barkolorious/opaque/report/ekler/PrMd_sch.pdf

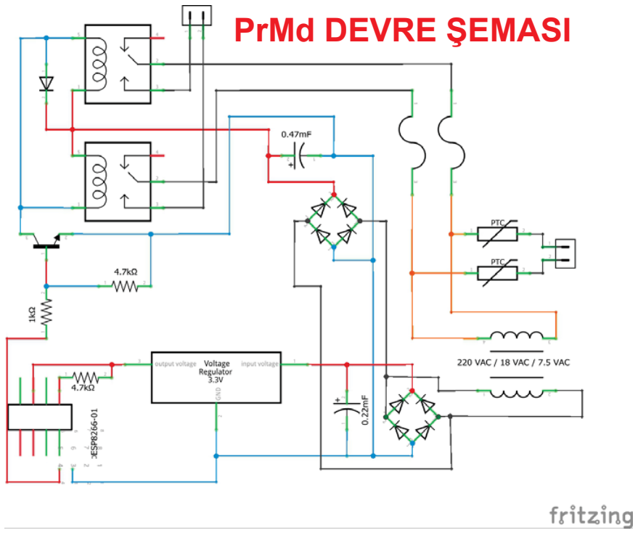
[picture p46: figure]
PrMd DEVRE ùEMASI
