barkolorious/opaque/Resimler/PCB_R4 V2.pdf

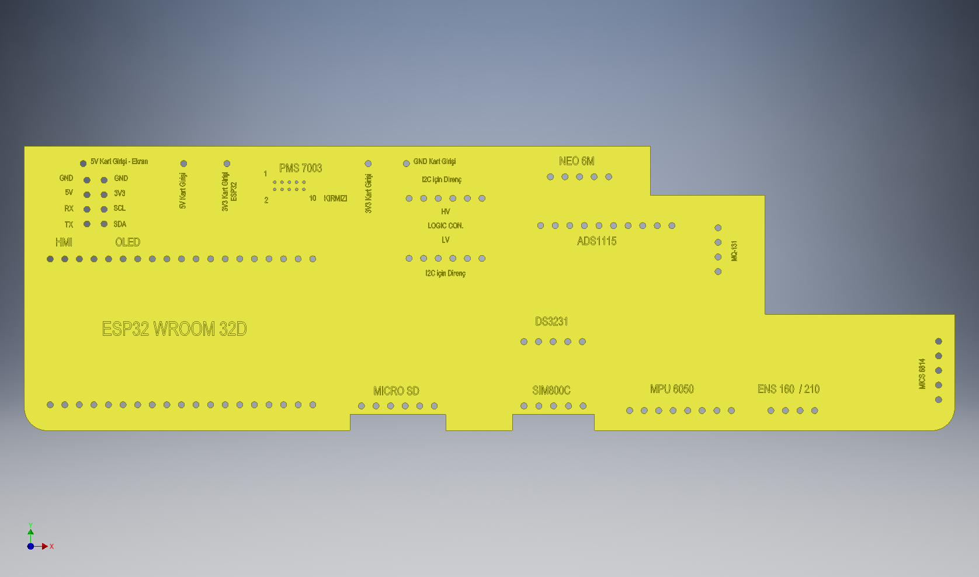
[picture p61: page 1]
