barkolorious/opaque/Notes/assets/20241108_101346.jpg

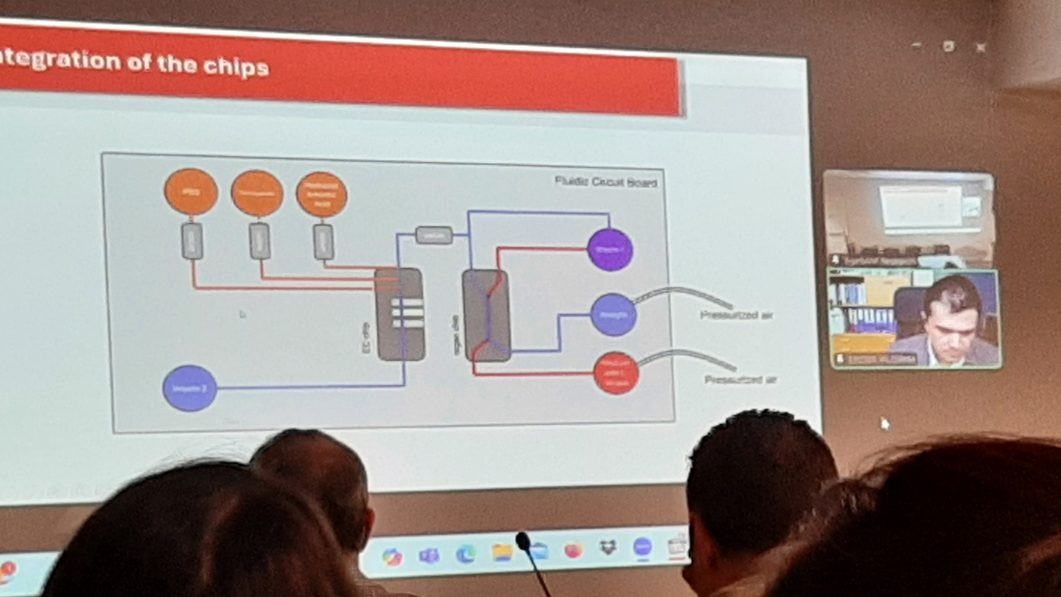
Notes/assets/20241108_101346.jpg
