barkolorious/opaque/Notes/assets/20241108_101506.jpg

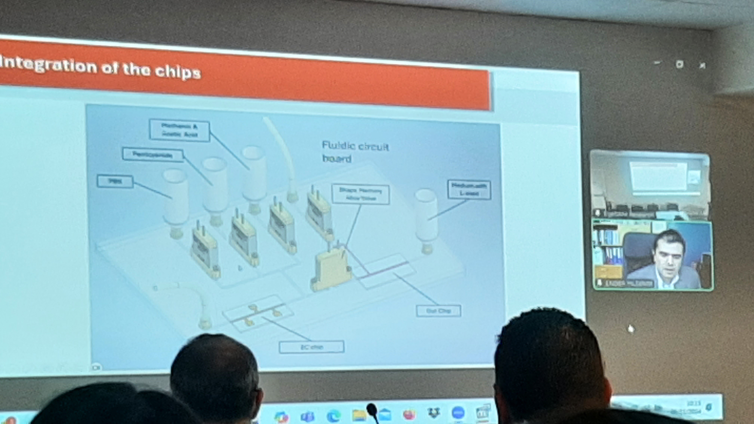
Notes/assets/20241108_101506.jpg
