barkolorious/opaque/Notes/assets/20241108_112509.jpg

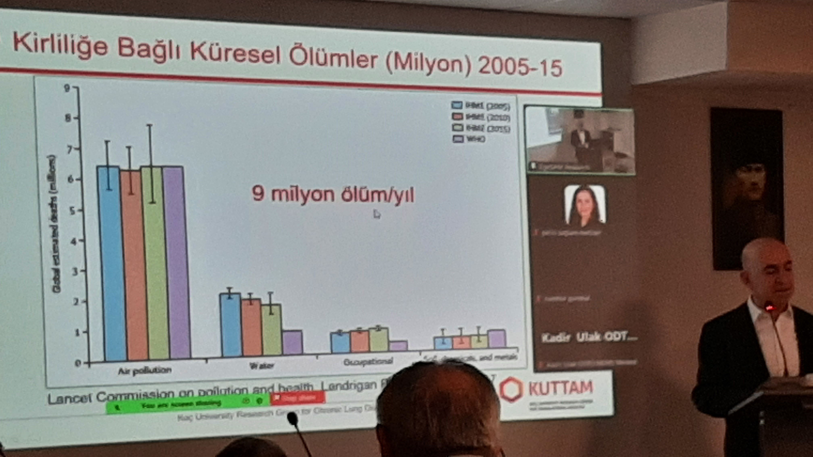
Notes/assets/20241108_112509.jpg
