barkolorious/opaque/Notes/assets/20241108_112550.jpg

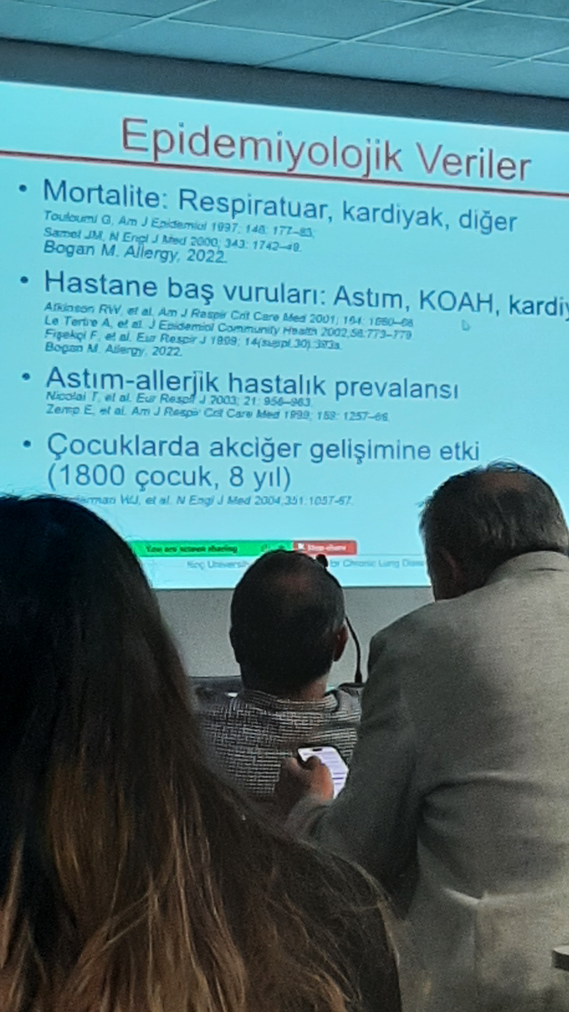
Notes/assets/20241108_112550.jpg
