barkolorious/opaque/Notes/assets/20241108_112724.jpg

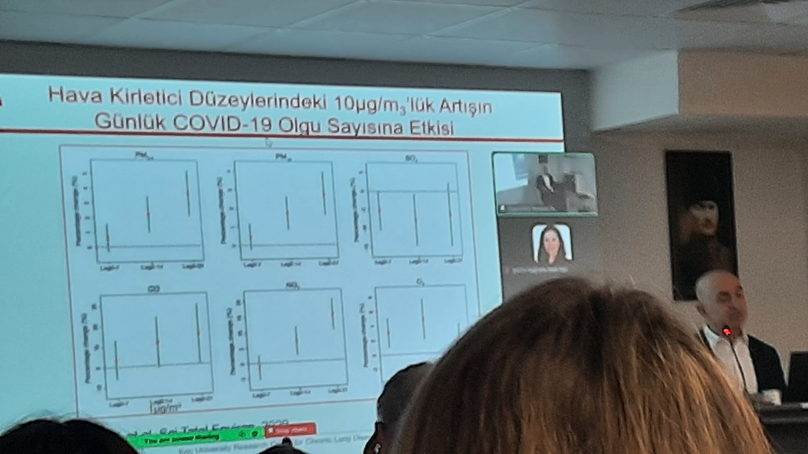
Notes/assets/20241108_112724.jpg
