barkolorious/opaque/Notes/assets/20241108_112844.jpg

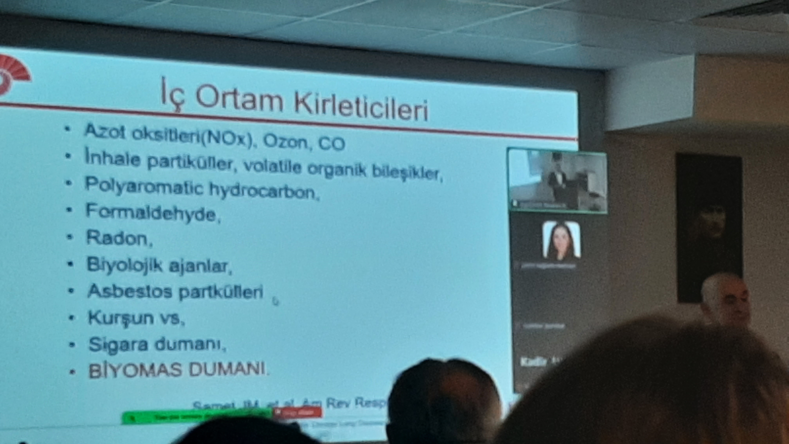
Notes/assets/20241108_112844.jpg
