barkolorious/opaque/Notes/assets/20241108_140740.jpg

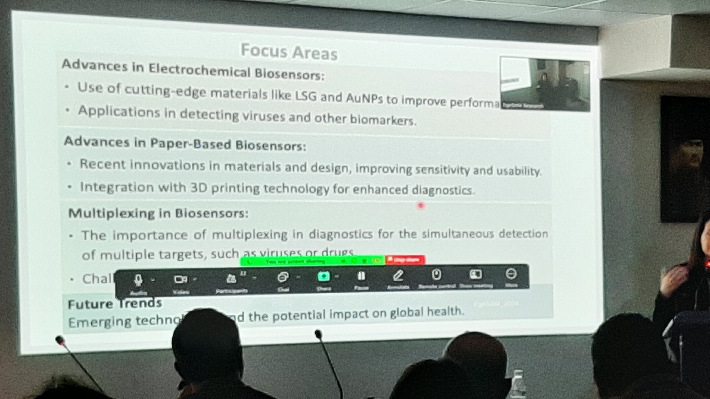
Notes/assets/20241108_140740.jpg
