barkolorious/opaque/Resimler/bandicam 2024-11-22 22-07-47-791.jpg

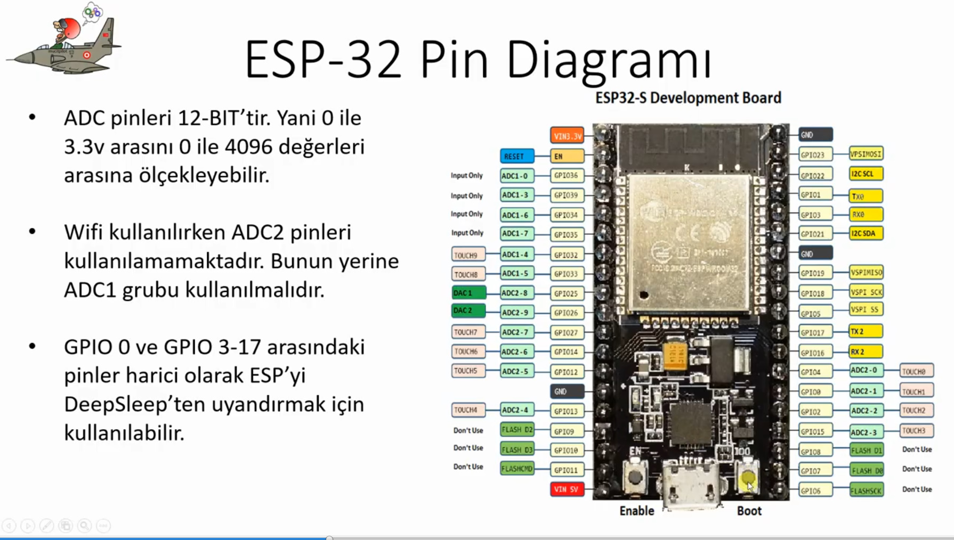
Resimler/bandicam 2024-11-22 22-07-47-791.jpg
