barkolorious/opaque/Resimler/bandicam 2024-11-25 14-44-11-441.jpg

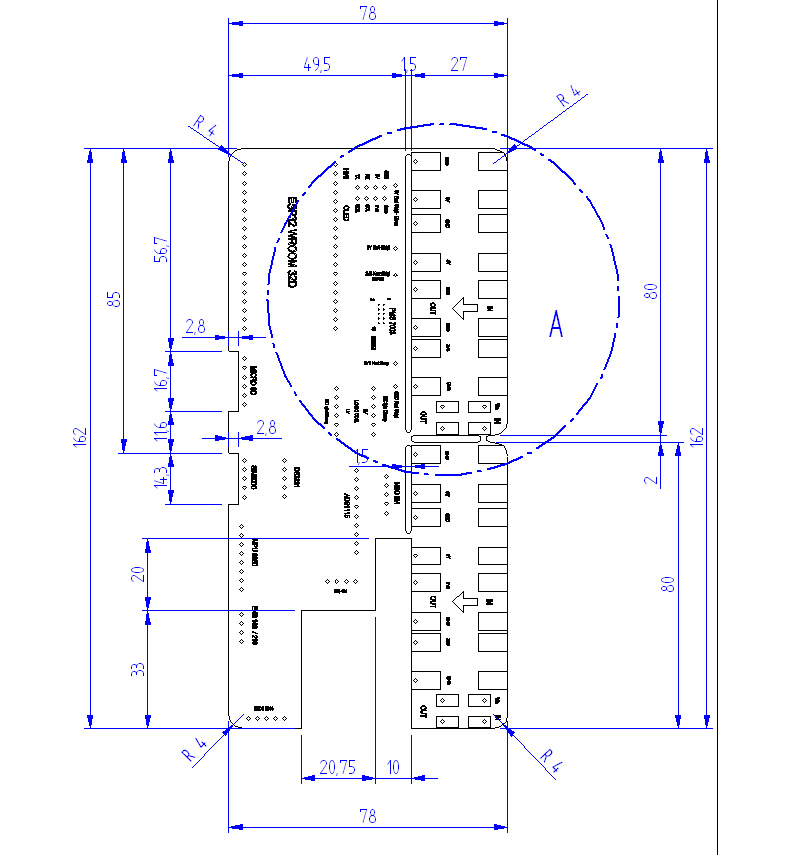
Resimler/bandicam 2024-11-25 14-44-11-441.jpg
