barkolorious/opaque/Resimler/bandicam 2024-11-25 14-45-46-956.jpg

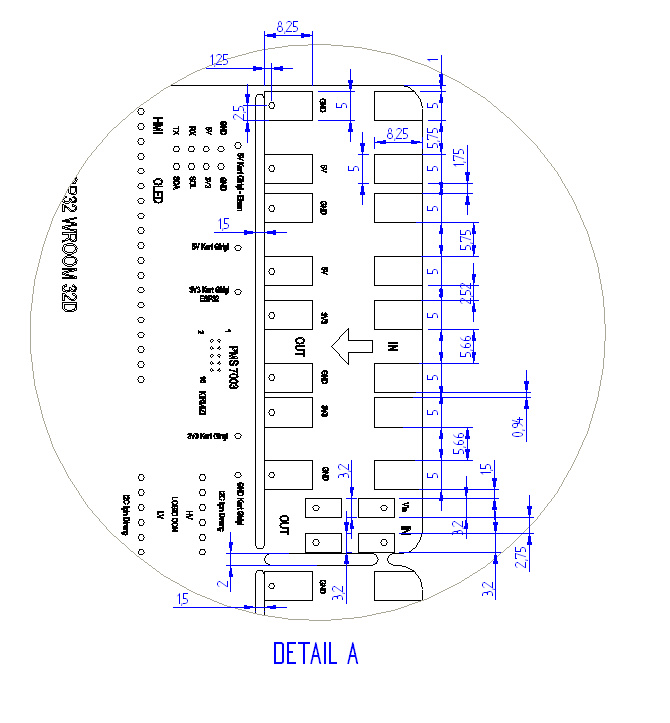
Resimler/bandicam 2024-11-25 14-45-46-956.jpg
