barkolorious/opaque/Resimler/bandicam 2024-11-25 14-51-43-470.jpg

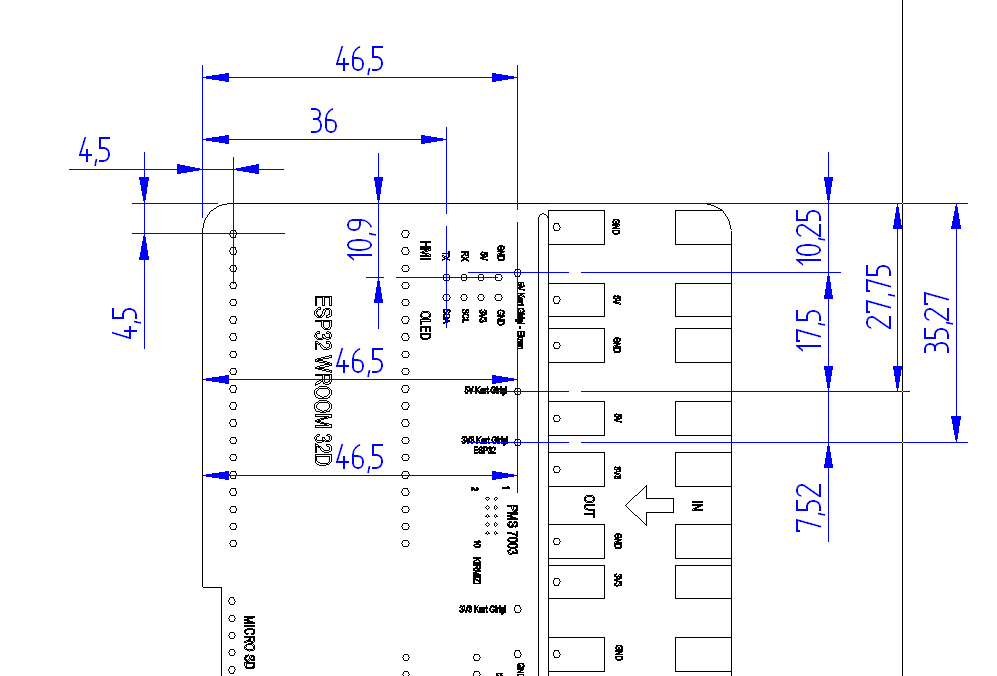
Resimler/bandicam 2024-11-25 14-51-43-470.jpg
