barkolorious/opaque/Resimler/bandicam 2024-11-25 14-54-14-675.jpg

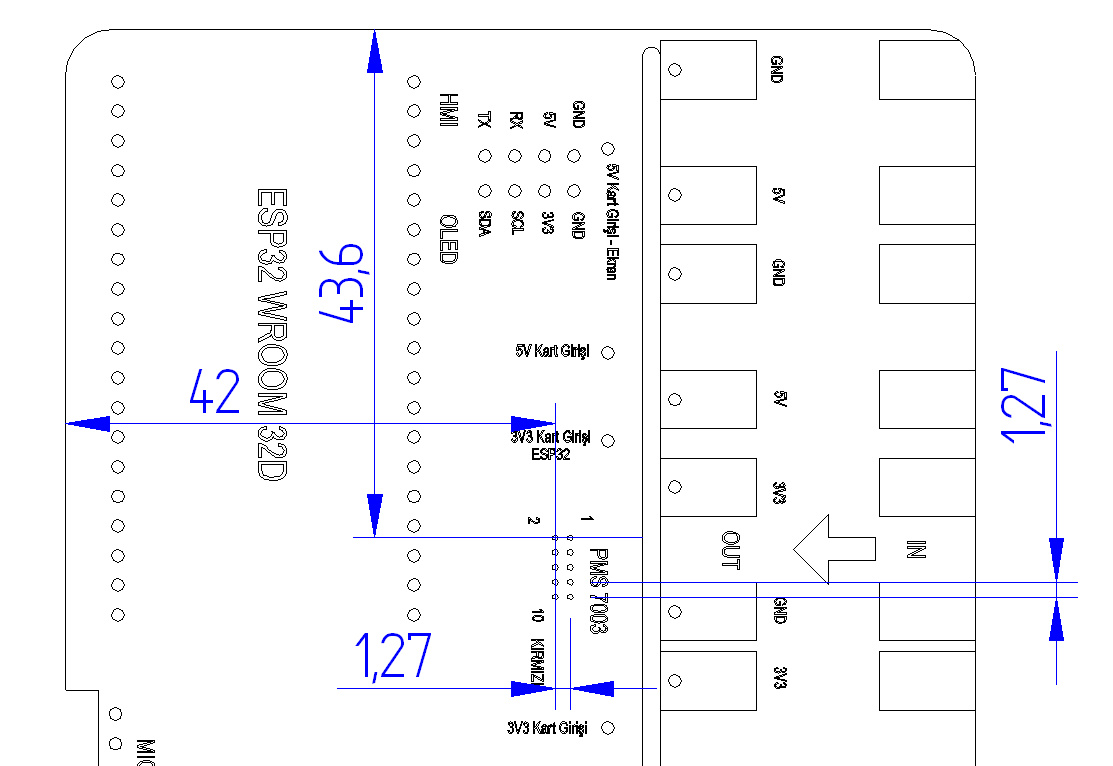
Resimler/bandicam 2024-11-25 14-54-14-675.jpg
