barkolorious/opaque/Resimler/bandicam 2024-11-25 15-03-01-337.jpg

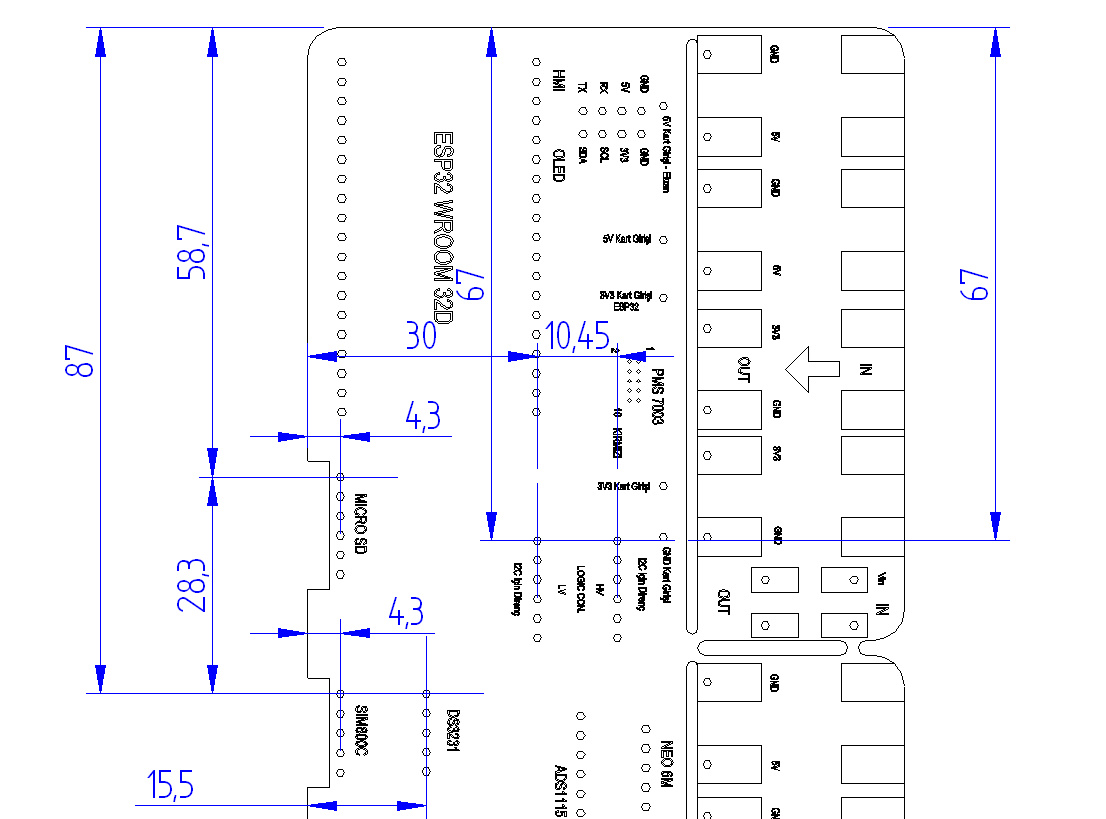
Resimler/bandicam 2024-11-25 15-03-01-337.jpg
