barkolorious/opaque/Resimler/bandicam 2024-11-25 15-12-23-431.jpg

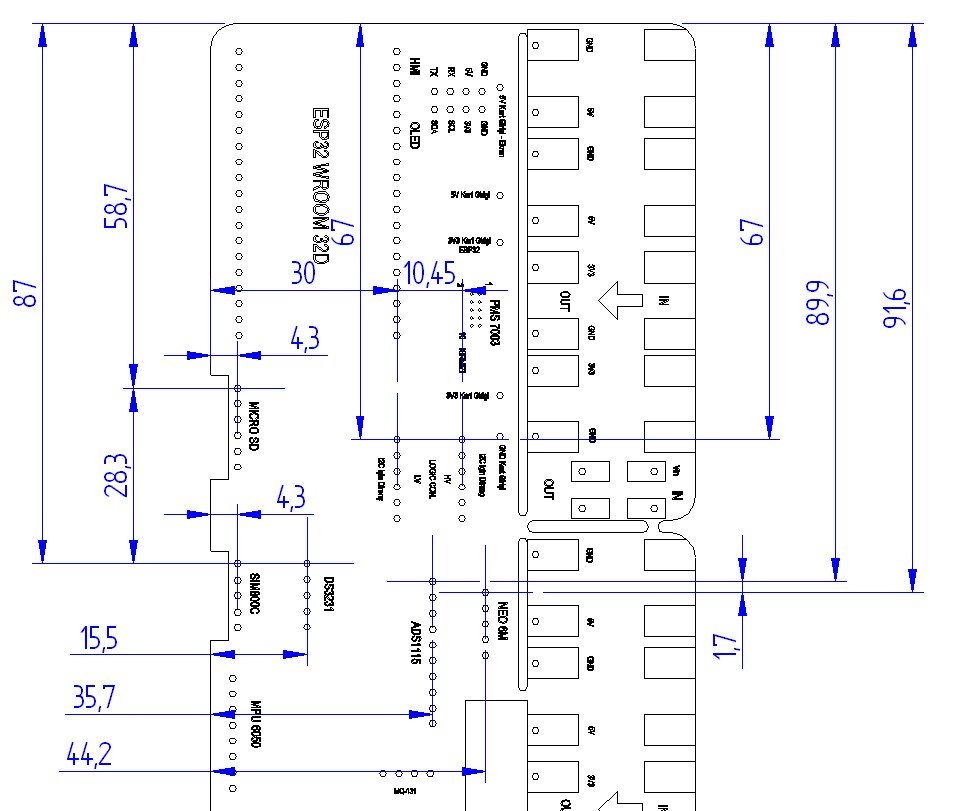
Resimler/bandicam 2024-11-25 15-12-23-431.jpg
