barkolorious/opaque/Resimler/bandicam 2024-11-25 15-30-23-947.jpg

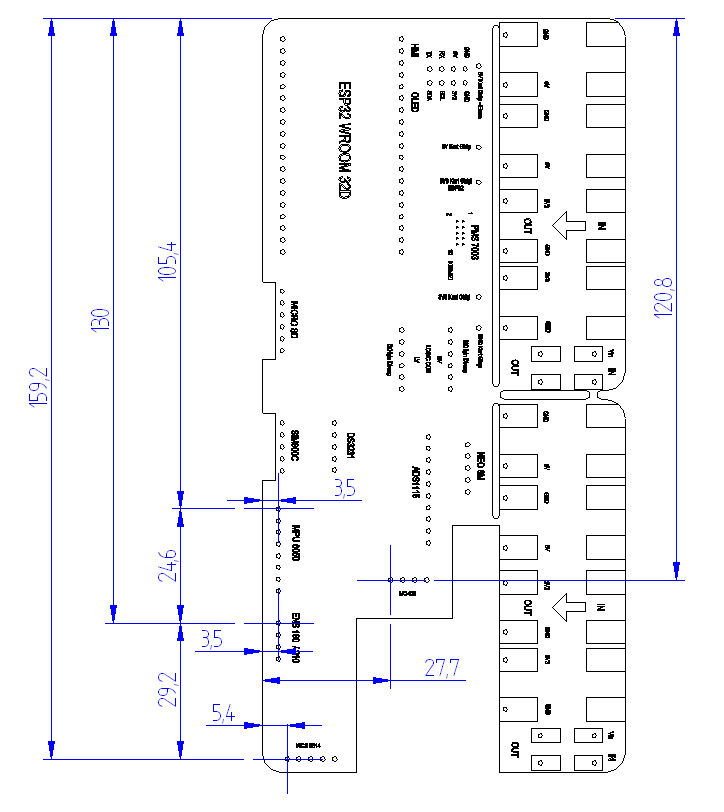
Resimler/bandicam 2024-11-25 15-30-23-947.jpg
