barkolorious/opaque/Resimler/resim.jpg

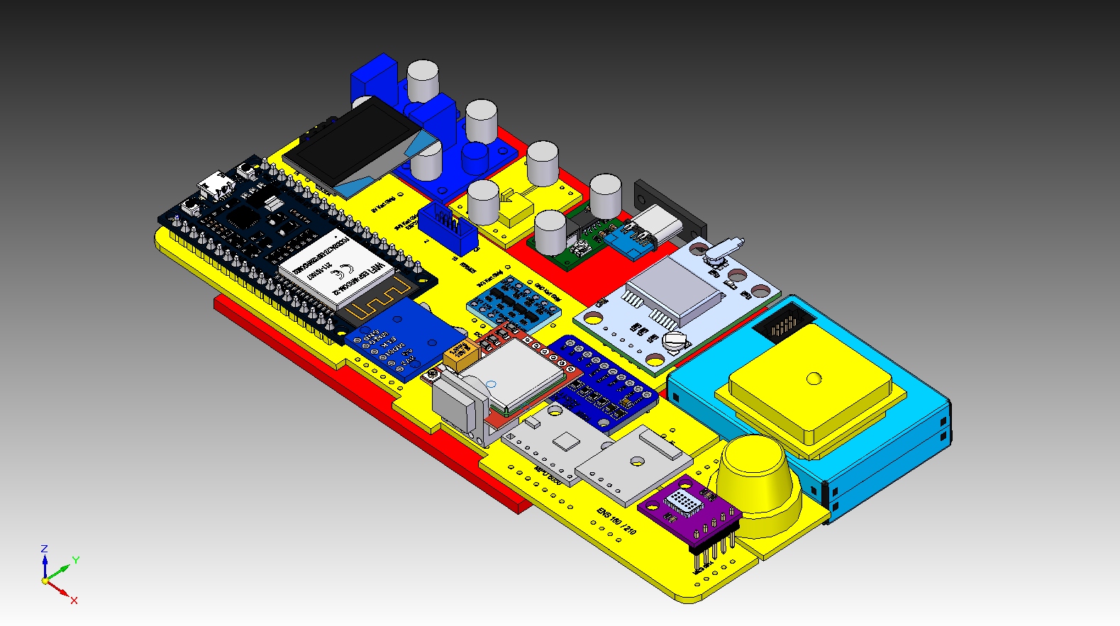
Resimler/resim.jpg
