barkolorious/opaque/Software/medical_kit/medical_kit-v1.01/ads1115.ino

/////////////////////////////////// ADS1115 ////////////////////////////////////
void ads1115_init (void) {
  ssd1306_new_screen();
  ssd1306_print(F("ADS1115 starting... "));
  if (!ads1115.begin()) {
    ssd1306_println(F("failed"));
    for (;;) {}
  }
  ssd1306_println(F("done!"));
}

float ads1115_read (uint8_t pin) {
  int16_t adc = ads1115.readADC_SingleEnded(0);
  return ads1115.computeVolts(adc);
}
/////////////////////////////////// ADS1115 ////////////////////////////////////
