barkolorious/opaque/Software/medical_kit/medical_kit-v1.01/mpu6050.ino

/////////////////////////////////// MPU6050 ////////////////////////////////////
void mpu6050_init (void) {
  ssd1306_new_screen();
  ssd1306_print(F("MPU6050 starting... "));
  mpu6050.setAddress(0x69);
  if (mpu6050.begin()) {
    ssd1306_println(F("failed"));
    for (;;) {}
  }
  ssd1306_println(F("done!"));

  ssd1306_print(F("MPU6050 initializing... "));
  mpu6050.calcOffsets(true, true);
  ssd1306_println(F("done!"));
}

void mpu6050_read (void) {
  mpu6050.update();
  float x = mpu6050.getAccX();
  float y = mpu6050.getAccY();
  float z = mpu6050.getAccZ();
  float mag = sqrt(x * x + y * y + z * z);
  mpu6050_in_motion = (mag > MPU6050_DETECT_THRESHOLD);
  return;
}
/////////////////////////////////// MPU6050 ////////////////////////////////////
