barkolorious/opaque/Software/tests/ssd1306_test_1/ssd1306_test_1.ino

/**************************************************************************
 This is an example for our Monochrome OLEDs based on SSD1306 drivers

 Pick one up today in the adafruit shop!
 ------> http://www.adafruit.com/category/63_98

 This example is for a 128x64 pixel display using I2C to communicate
 3 pins are required to interface (two I2C and one reset).

 Adafruit invests time and resources providing this open
 source code, please support Adafruit and open-source
 hardware by purchasing products from Adafruit!

 Written by Limor Fried/Ladyada for Adafruit Industries,
 with contributions from the open source community.
 BSD license, check license.txt for more information
 All text above, and the splash screen below must be
 included in any redistribution.
 **************************************************************************/

#include <SPI.h>
#include <Wire.h>
#include <Adafruit_GFX.h>
#include <Adafruit_SSD1306.h>

#define SCREEN_WIDTH 128 // OLED display width, in pixels
#define SCREEN_HEIGHT 64 // OLED display height, in pixels

// Declaration for an SSD1306 display connected to I2C (SDA, SCL pins)
// The pins for I2C are defined by the Wire-library. 
// On an arduino UNO:       A4(SDA), A5(SCL)
// On an arduino MEGA 2560: 20(SDA), 21(SCL)
// On an arduino LEONARDO:   2(SDA),  3(SCL), ...
#define OLED_RESET     -1 // Reset pin # (or -1 if sharing Arduino reset pin)
#define SCREEN_ADDRESS 0x3C ///< See datasheet for Address; 0x3D for 128x64, 0x3C for 128x32
Adafruit_SSD1306 display(SCREEN_WIDTH, SCREEN_HEIGHT, &Wire, OLED_RESET);

#define LOGO_HEIGHT   10
#define LOGO_WIDTH    20
// 'opaque_logo', 128x64px
const unsigned char logo_opaque [] PROGMEM = {
	0x7f, 0xff, 0xe3, 0xff, 0xff, 0x1f, 0xff, 0xf8, 0xff, 0xff, 0xcc, 0x00, 0x03, 0x3f, 0xff, 0xf0, 
	0xff, 0xff, 0xf7, 0xff, 0xff, 0xbf, 0xff, 0xfd, 0xff, 0xff, 0xec, 0x00, 0x03, 0x7f, 0xff, 0xf8, 
	0xc0, 0x00, 0x36, 0x00, 0x01, 0x80, 0x00, 0x0d, 0x80, 0x00, 0x6c, 0x00, 0x03, 0x60, 0x00, 0x18, 
	0xc0, 0x00, 0x36, 0x00, 0x01, 0x80, 0x00, 0x0d, 0x80, 0x00, 0x6c, 0x00, 0x03, 0x60, 0x00, 0x18, 
	0xc0, 0x00, 0x36, 0x00, 0x01, 0x9f, 0xff, 0xfd, 0x80, 0x00, 0x6c, 0x00, 0x03, 0x7f, 0xff, 0xf8, 
	0xc0, 0x00, 0x36, 0x00, 0x01, 0xbf, 0xff, 0xfd, 0x80, 0x00, 0x6c, 0x00, 0x03, 0x7f, 0xff, 0xf0, 
	0xc0, 0x00, 0x36, 0x00, 0x01, 0xb0, 0x00, 0x0d, 0x80, 0x00, 0x6c, 0x00, 0x03, 0x60, 0x00, 0x00, 
	0xc0, 0x00, 0x36, 0x00, 0x01, 0xb0, 0x00, 0x0d, 0x80, 0x00, 0x6c, 0x00, 0x03, 0x60, 0x00, 0x00, 
	0xff, 0xff, 0xf7, 0xff, 0xff, 0xbf, 0xff, 0xfd, 0xff, 0xff, 0xef, 0xff, 0xff, 0x7f, 0xff, 0xf8, 
	0x7f, 0xff, 0xe7, 0xff, 0xff, 0x1f, 0xff, 0xf8, 0xff, 0xff, 0xe7, 0xff, 0xfe, 0x3f, 0xff, 0xf0, 
	0x00, 0x00, 0x06, 0x00, 0x00, 0x00, 0x00, 0x00, 0x00, 0x00, 0x60, 0x00, 0x00, 0x00, 0x00, 0x00, 
	0x00, 0x00, 0x06, 0x00, 0x00, 0x00, 0x00, 0x00, 0x00, 0x00, 0x60, 0x00, 0x00, 0x00, 0x00, 0x00, 
	0x00, 0x00, 0x06, 0x00, 0x00, 0x00, 0x00, 0x00, 0x00, 0x00, 0x60, 0x00, 0x00, 0x00, 0x00, 0x00, 
	0x00, 0x00, 0x06, 0x00, 0x00, 0x00, 0x00, 0x00, 0x00, 0x00, 0x60, 0x00, 0x00, 0x00, 0x00, 0x00, 
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
  // display.display(). These examples demonstrate both approaches...

  //testdrawchar();      // Draw characters of the default font
}

void loop() {
  testanim();
  display.
  delay(1000);
}

void testdrawchar(void) {
  display.clearDisplay();

  display.getTextBounds()

  display.setTextSize(1);      // Normal 1:1 pixel scale
  display.setTextColor(SSD1306_WHITE); // Draw white text
  display.setCursor(0, 0);     // Start at top-left corner
  //display.cp437(true);         // Use full 256 char 'Code Page 437' font
  display.setFont();

  // Not all the characters will fit on the display. This is normal.
  // Library will draw what it can and the rest will be clipped.
  for(int16_t i=65; i<91; i++) {
    display.write(i);
  }

  display.write(' ');

  for(int16_t i=97; i<123; i++) {
    display.write(i);
  }

  display.display();
  delay(2000);
}

void testanim (void) {
  // display.drawBitmap(0, 0, myBitmap, 128, 64, WHITE);
  display.clearDisplay();
  display.display();
  delay(100);
  display.drawBitmap(2, 27, logo_o, LOGO_WIDTH, LOGO_HEIGHT, SSD1306_WHITE);
  display.display();
  delay(100);
  display.drawBitmap(23, 27, logo_o, LOGO_WIDTH, LOGO_HEIGHT, SSD1306_WHITE);
  display.display();
  delay(100);
  display.drawBitmap(44, 27, logo_o, LOGO_WIDTH, LOGO_HEIGHT, SSD1306_WHITE);
  display.display();
  delay(100);
  display.drawBitmap(65, 27, logo_o, LOGO_WIDTH, LOGO_HEIGHT, SSD1306_WHITE);
  display.display();
  delay(100);
  display.drawBitmap(86, 27, logo_o, LOGO_WIDTH, LOGO_HEIGHT, SSD1306_WHITE);
  display.display();
  delay(100);
  display.drawBitmap(107, 27, logo_o, LOGO_WIDTH, LOGO_HEIGHT, SSD1306_WHITE);
  display.display();
  delay(150);
  display.clearDisplay();
  display.drawBitmap(2, 27, logo_opaque_half, 125, 15, SSD1306_WHITE);
  display.display();
  delay(75);
  display.clearDisplay();
  display.drawBitmap(2, 27, logo_opaque, 125, 15, SSD1306_WHITE);
  display.display();
}
