barkolorious/opaque/Software/tests/esp32_button_test_1/esp32_button_test_1.ino

int dugme1 = 32, dugme2 = 33;

void setup () {
  Serial.begin(115200);

  pinMode(dugme1, INPUT);
  pinMode(dugme2, INPUT);
                                                          
  Serial.println("started...");
}


void loop () {
  int deger1 = digitalRead(dugme1);
  int deger2 = digitalRead(dugme2);

  Serial.print("dgr_1:");Serial.print(deger1);
  Serial.print(",dgr_2:");Serial.println(deger2);
}
