barkolorious/opaque/Software/tests/esp32_ens160-ens210_test_1/esp32_ens160-ens210_test_1.ino

/*
+-----------------+--------+
| ENS160 + ENS210 | ESP32  |
+=================+========+
| GND             | GND    |
| VCC             | 3V3    |
| SDA             | GPIO21 |
| SCL             | GPIO22 |
+-----------------+--------+
*/

#include <Arduino.h>
#include <Wire.h>
#include "ens210.h"
#include "SparkFun_ENS160.h"

ENS210 ens210;

SparkFun_ENS160 ens160; 
int ensStatus; 

void setup() {
	Serial.begin(115200);
  Wire.begin();

  /* ---------------- ENS210 --------------- */
  ens210.begin();
  ens210.init();

  if (ens210.isConnected() == false) {
    Serial.println("Error -- The ENS210 is not connected.");
    return;
  }

  Serial.print("Starting continous mode..");
  while (ens210.startContinuousMeasure() != RESULT_OK) {
    Serial.print(".");
    delay(ENS21X_SYSTEM_TIMING_BOOTING);
  }
  Serial.println(" Done!");

  Serial.println();
  Serial.println("----------------------------------------");

  /* ---------------- ENS160 --------------- */

  if (!ens160.begin() ) {
		Serial.println("Could not communicate with the ENS160, check wiring.");
		return;
	}

  Serial.println("Example 1 Basic Example.");

	// Reset the indoor air quality sensor's settings.
	if (ens160.setOperatingMode(SFE_ENS160_RESET)) Serial.println("Ready.");

	delay(100);

  ens160.setOperatingMode(SFE_ENS160_STANDARD);
  ensStatus = ens160.getFlags();
	Serial.print("Gas Sensor Status Flag (0 - Standard, 1 - Warm up, 2 - Initial Start Up): ");
	Serial.println(ensStatus);
}

void loop() {
  /* ---------------- ENS210 --------------- */
  ens210.wait();
  if (ens210.update() == RESULT_OK) {
    float temperatureCelsius = ens210.getTempCelsius();
    float humidityPercent    = ens210.getHumidityPercent();

    Serial.print("T:");
    Serial.print(temperatureCelsius);
    Serial.print("°C\t");

    Serial.print("Humidity:");
    Serial.print(humidityPercent);
    Serial.println("%");
  }

  /* ---------------- ENS160 --------------- */
  if( ens160.checkDataStatus() )	{
		Serial.print("AQI (1-5) : ");
		Serial.println(ens160.getAQI());

		Serial.print("tVOC: ");
		Serial.print(ens160.getTVOC());
		Serial.println("ppb");

		Serial.print("eCO2: ");
		Serial.print(ens160.getECO2());
		Serial.println("ppm");

	  Serial.print("Gas Sensor Status Flag (0 - Standard, 1 - Warm up, 2 - Initial Start Up): ");
    Serial.println(ens160.getFlags());

		Serial.println();
	}

	delay(200);
}
