barkolorious/opaque/Software/tests/mpu6050_test_1/mpu6050_test_1.ino

#include <Adafruit_MPU6050.h>
#include <Adafruit_Sensor.h>
#include <Wire.h>

Adafruit_MPU6050 mpu;

void setup(void) {
  Serial.begin(115200);
  while (!Serial)
    delay(10); // will pause Zero, Leonardo, etc until serial console opens

  Serial.println("Adafruit MPU6050 test!");

  // Try to initialize!
  if (!mpu.begin()) {
    Serial.println("Failed to find MPU6050 chip");
    while (1) {
      delay(10);
    }
  }
  Serial.println("MPU6050 Found!");

  //setupt motion detection
  mpu.setHighPassFilter(MPU6050_HIGHPASS_0_63_HZ);
  mpu.setMotionDetectionThreshold(3);
  mpu.setMotionDetectionDuration(5);
  mpu.setInterruptPinLatch(true);	// Keep it latched.  Will turn off when reinitialized.
  mpu.setInterruptPinPolarity(true);
  mpu.setMotionInterrupt(true);

  Serial.println("");
  delay(100);
}

void loop() {
  sensors_event_t a, g, temp;
  mpu.getEvent(&a, &g, &temp);

  float x = a.acceleration.x;
  float y = a.acceleration.y;
  float z = a.acceleration.z;
  float magnitude = sqrt(x * x + y * y + z * z) - 10.30;
  Serial.print("Mag:");
  Serial.print(magnitude);
  Serial.print(",upper:");
  Serial.print(10);
  Serial.print(",lower:");
  Serial.print(-2);
  Serial.print(",motion:");
  if (mpu.getMotionInterruptStatus()) {
    Serial.println(1);
  } else Serial.println(0);
  

  delay(10);
}
