barkolorious/opaque/Software/tests/mpu6050_test_2/mpu6050_test_2.ino

/* Get all possible data from MPU6050
 * Accelerometer values are given as multiple of the gravity [1g = 9.81 m/s²]
 * Gyro values are given in deg/s
 * Angles are given in degrees
 * Note that X and Y are tilt angles and not pitch/roll.
 *
 * License: MIT
 */

#include "Wire.h"
#include <MPU6050_light.h>
#define MPU6050_DETECT_THRESHOLD 1.3

MPU6050 mpu(Wire);

void setup() {
  Serial.begin(9600);
  Wire.begin();
  
  if (mpu.begin()) {
    Serial.println(F("initialization failed! (MPU6050)"));
    Serial.flush();
    return;
  }

  Serial.println(F("calibrating MPU6050"));
  delay(1000);
  mpu.calcOffsets(true,true); // gyro and accelero
  Serial.println(F("calibration done! (MPU6050)"));
}

void loop() {
  uint8_t is_in_motion = mpu6050_is_in_motion();
  Serial.print("motion:");
  Serial.println(is_in_motion);
}

uint8_t mpu6050_is_in_motion (void) {
  mpu.update();
  float x = mpu.getAccX();
  float y = mpu.getAccY();
  float z = mpu.getAccZ();
  float mag = sqrt(x * x + y * y + z * z);
  return (mag > MPU6050_DETECT_THRESHOLD);
}
